BPTRobotics/bptrobotics-fe-26--wro/slovenia_2025/img/else/545f1089-10ea-429a-9157-808c22101ddc.jpg

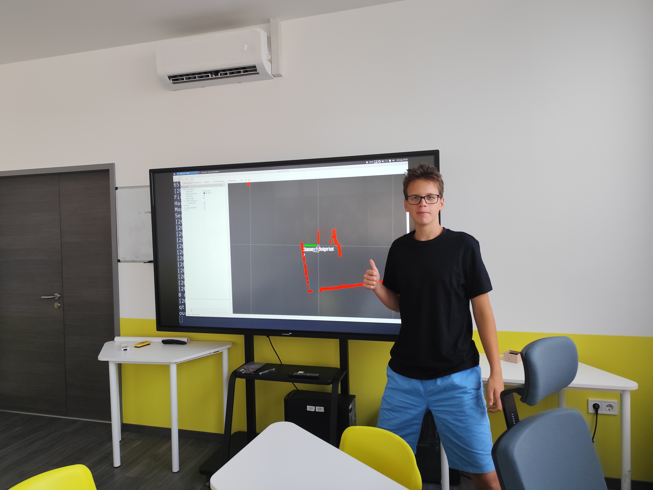
slovenia_2025/img/else/545f1089-10ea-429a-9157-808c22101ddc.jpg
