BPTRobotics/bptrobotics-fe-26--wro/slovenia_2025/img/else/IMG_20250808_084030.jpg

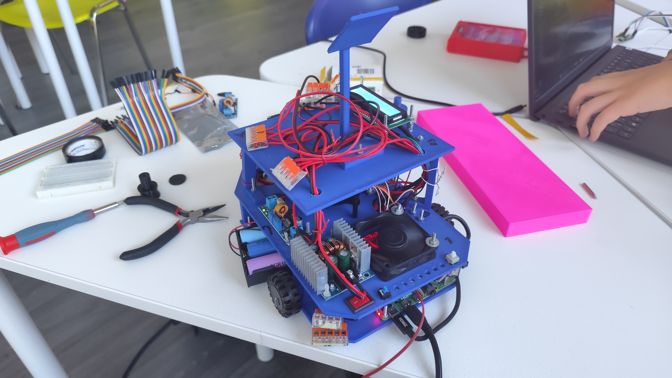
slovenia_2025/img/else/IMG_20250808_084030.jpg
