BPTRobotics/bptrobotics-fe-26--wro/slovenia_2025/img/else/IMG_20250823_171950.jpg

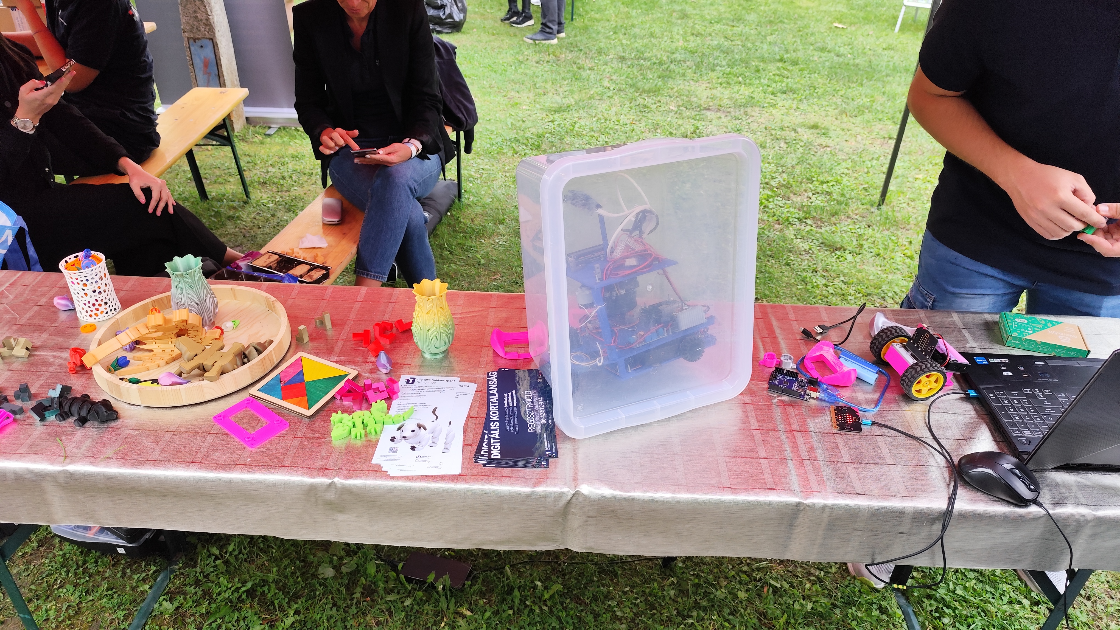
slovenia_2025/img/else/IMG_20250823_171950.jpg
