BPTRobotics/bptrobotics-fe-26--wro/slovenia_2025/img/robots/Robot Casual (16).jpg

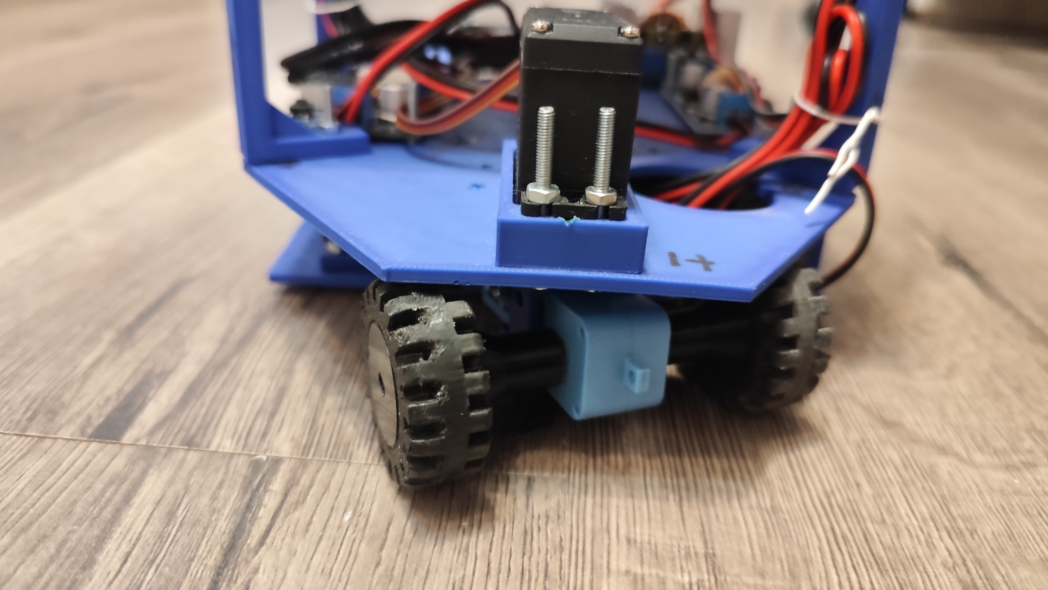
slovenia_2025/img/robots/Robot Casual (16).jpg
