BPTRobotics/bptrobotics-fe-26--wro/slovenia_2025/img/Team/Funny (2).jpg

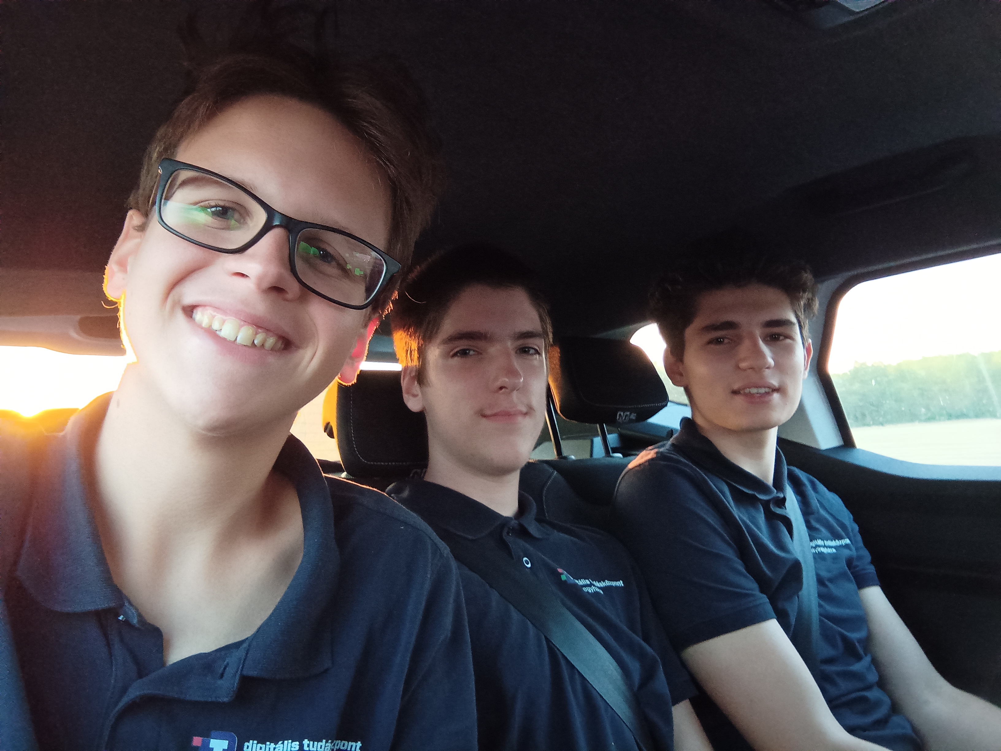
slovenia_2025/img/Team/Funny (2).jpg
